glikely/openscad-arcade/materials.scad

paper_sizes = [
	["A0", [1189,841]],
	["A1", [841,594]],
	["A2", [594,420]],
	["A3", [420,297]],
	["A4", [297,210]]
];

mdf_thick = 25.4 * 3 / 4;
plex_thick = 3;

// Materials
Oak = [0.65, 0.5, 0.4];
Pine = [0.85, 0.7, 0.45];
Birch = [0.9, 0.8, 0.6];
FiberBoard = [0.7, 0.67, 0.6];
BlackPaint = [0.2, 0.2, 0.2];
Iron = [0.36, 0.33, 0.33];
Steel = [0.65, 0.67, 0.72];
Stainless = [0.45, 0.43, 0.5];
Aluminum = [0.77, 0.77, 0.8];
Brass = [0.88, 0.78, 0.5];
Transparent = [1, 1, 1, 0.2];
